wenzel-lab/light-sheet-microscope/adjustable_slit.md

# Adjustable Slit
Cube insert

{{BOM}}

[M3 x 5mm screw]: parts/mech/M3-5.md "{cat:mechanic}"
[M3 x 25mm HEX screw]: parts/mech/HEX-M3-25.md "{cat:mechanic}"
[Nut]: parts/mech/nuts.md "{cat:mechanic}"
[Blades]: parts/mech/blade.md "{cat:mechanic}"

[2.5mm Ball-end Allen key]: parts/tools/2.5mmBallEndAllenKey.md "{cat:tool}"

[Compliant-slit flex - cap]: models/Adjustable_slit/Compliant_slit_insert_V2-cap_layer.stl "{previewpage}"
[Compliant-slit flex - layer 1]: models/Adjustable_slit/Compliant_slit_insert_V2-flex_layer1.stl "{previewpage}"
[Compliant-slit flex - layer 2]: models/Adjustable_slit/Compliant_slit_insert_V2-flex_layer2.stl "{previewpage}"
[Slit Knob]: models/Adjustable_slit/Adjustable-Slit-Knob.stl "{previewpage}"



This flex mechanism helps to control the pass of the light beam by adjusting the top knob.

>! This component is still being tested

#Assembly

## Step 1:
Take the [Compliant-slit flex - layer 1]{qty: 1, cat: PrintedPart} and join it with the [Compliant-slit flex - layer 2]{qty: 1, cat: PrintedPart}, leaving the [Blades]{qty:1} and the [HEX screw][M3 x 25mm HEX screw]{qty:1} in the middle of them. The idea is to leave captured the head of the screw and the sharp edges of the blades in the center.

## Step 2;
Put two [M3 x 5mm screw]{qty: 1} through the assembled piece to hold the blades previously inserted and tight with the [2.5mm Ball-end Allen key]{qty:1}.

## Step 3:
Place the [cap][Compliant-slit flex - cap]{qty: 1, cat: PrintedPart}, closing the mechanism.

## Step 4:
Paste the [Knob][Slit Knob]{qty: 1, cat: PrintedPart} with the screw tip using a strong glue.

##Step 5: Put it in a cube!

Take one of your [UC2 cubes](UC2files.md) and place your assembled piece in it. You can purchase the cube or 3D print it, either option works fine.
