wenzel-lab/light-sheet-microscope/control-Interface.md

# Laser Control Interface

##To assemble this piece, go to our "laser illumination" documentation

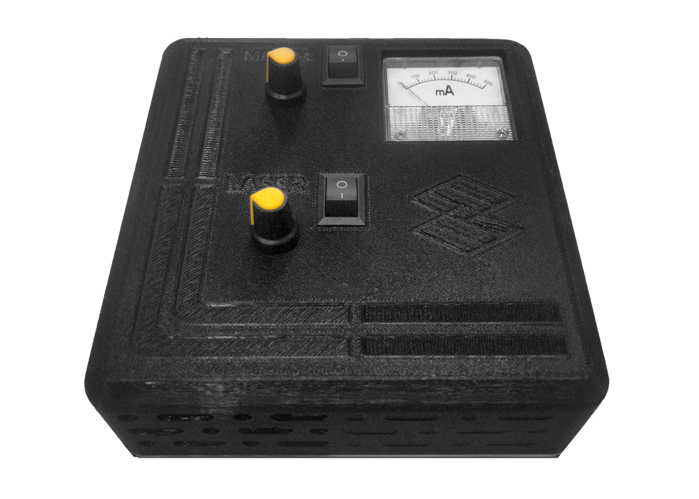
[picture p37: images/control-Interface/control-Interface.jpg]


##

>i **[Link](https://librehub.github.io/fiber-coupled-laser-illumination/assembly.html)** 
>i
>i [Low-cost, modular fiber-coupled laser illumination](https://librehub.github.io/fiber-coupled-laser-illumination/assembly.html)
