wenzel-lab/light-sheet-microscope/Power_lens_XY_aligner.md

# Power Lens XY aligner

Cube insert

{{BOM}}

[M3 x 25 mm hex head screw]: parts/mech/HEX-M3-25.md "{cat:mechanic}"

[Heat insert]: parts/mech/Hinsert.md "{cat:mechanic}"

[Soldering iron]: parts/tools/soldiron.md "{cat:tool}"

[Linear Beam Generator Lens]: parts/optics/Linear-beam-generator-lens.md "{cat:optical}"

[Power Lens XY aligner base]: models/Power-Lense-XY-aligner/Power-Lens-XY-aligner-base.stl "{previewpage}"

[Power Lens XY aligner A-Adapter]:models/Power-Lense-XY-aligner/Power-Lens-XY-aligner-A-Adapter.stl "{previewpage}"



This component is designed to be used inside a UC2 cube, allowing for better laser beam positioning through XY control.

#Assembly: 
##Screws {pagestep}

- Place 2 [heat inserts][Heat insert]{qty:2} into the [XY aligner base][Power Lens XY aligner base]{qty: 1, cat:printedpart} using the [Soldering iron]{qty:1}

- Screw the [hex head screws][M3 x 25 mm hex head screw]{qty:2}



##Lens Adapter {pagestep}
Place the springs and screw the [A-Adapter][Power Lens XY aligner A-Adapter]{qty: 1, cat:printedpart} 



##Lens {pagestep}

Place the [Lens][Linear Beam Generator Lens]{qty:1}  in the  [A-Adapter].

>! **Caution** 
>!
>! Do not touch the lens directly to avoid getting it dirty or scratched.

## Put it in a cube!:{pagestep}

Take one of your [UC2 cubes](UC2files.md) and place your assembled piece in it. You can purchase the cube or 3D print it, either option works fine.
