wenzel-lab/light-sheet-microscope/Prepare.md

#Prepare the pieces

* ### [Print the plastic Parts](printing.md)

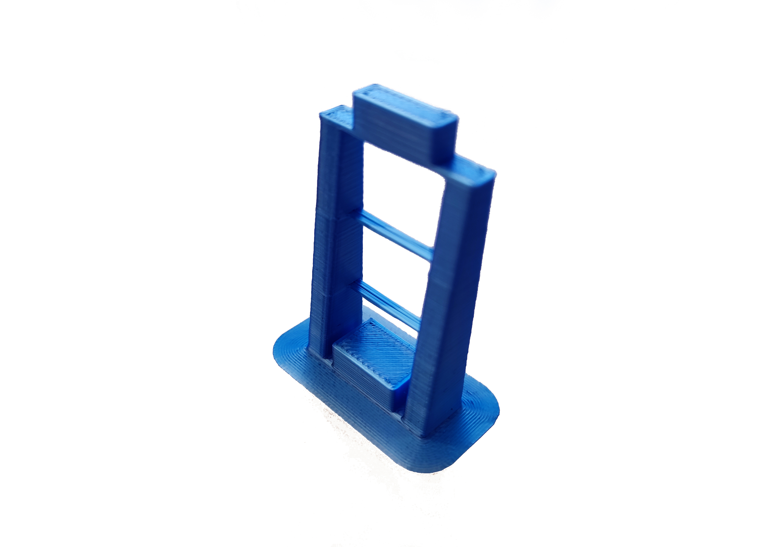
[picture p44: images/Tools-and-Parts/just_leg_test.jpg]


* ### [Sanding screw tips](Sanding.md)

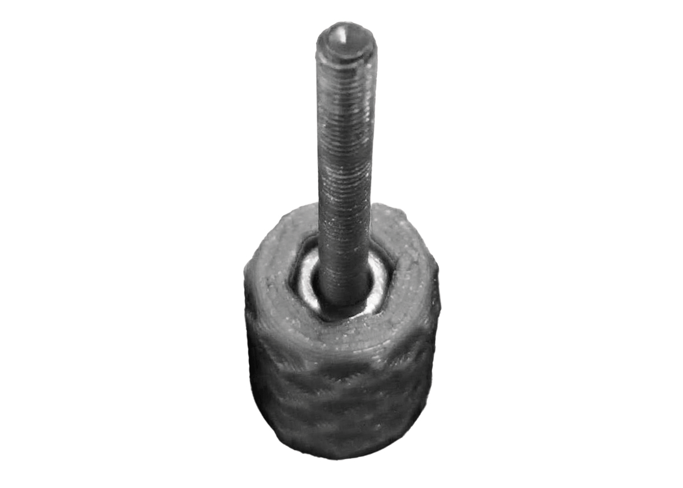
[picture p45: images/Sanding/sand.gif]
