wenzel-lab/light-sheet-microscope/images/Kinematic_Mirrors/Completed.jpg

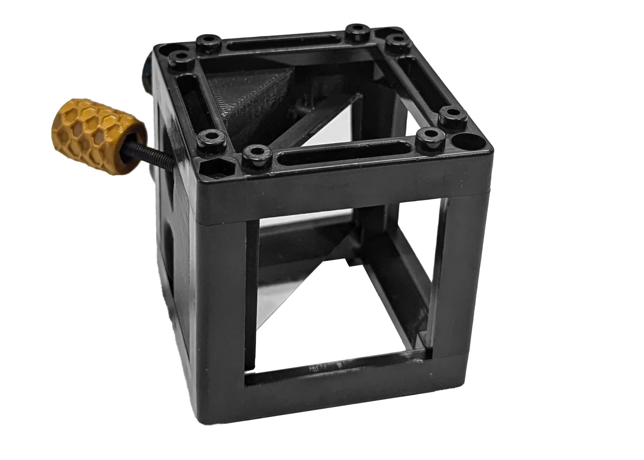
images/Kinematic_Mirrors/Completed.jpg
