wenzel-lab/light-sheet-microscope/images/Kinematic_Mirrors/Holder-and-Mirror.jpg

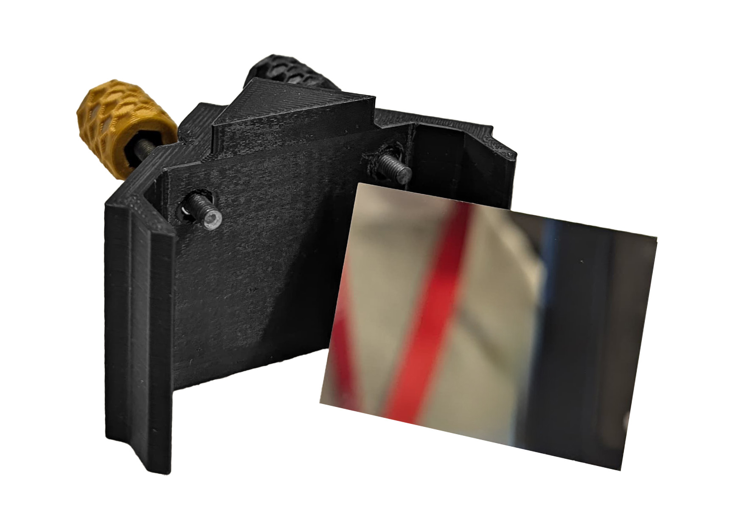
images/Kinematic_Mirrors/Holder-and-Mirror.jpg
