wenzel-lab/light-sheet-microscope/parts/tools/screwdriver.md

# Screwdriver

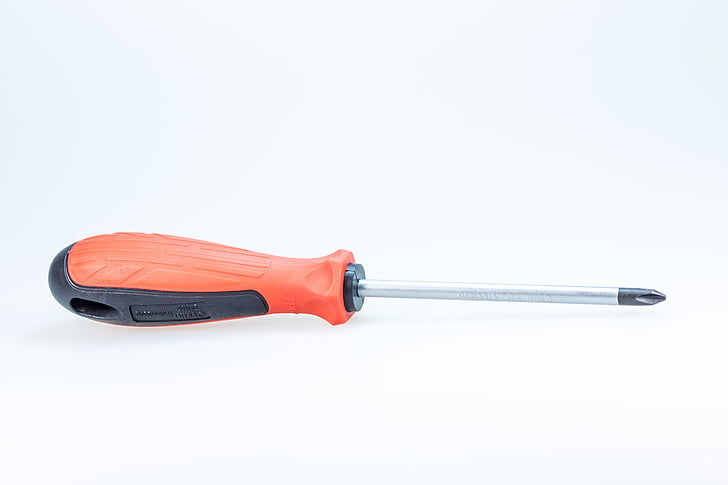
[picture p66: images/Tools-and-Parts/screwdriver.jpg]


*Supplier:* [Aliexpress](https://es.aliexpress.com/item/1005006019454539.html)
