wenzel-lab/light-sheet-microscope/parts/tools/soldiron.md

# Soldering iron

Handheld tool usually used for joining or repairing electronic components. It consists of a heated metal tip attached to a handle. The tip is heated using electrical power, typically supplied via a power cord. Soldering irons come in different wattage's and tip sizes to accommodate various soldering tasks.

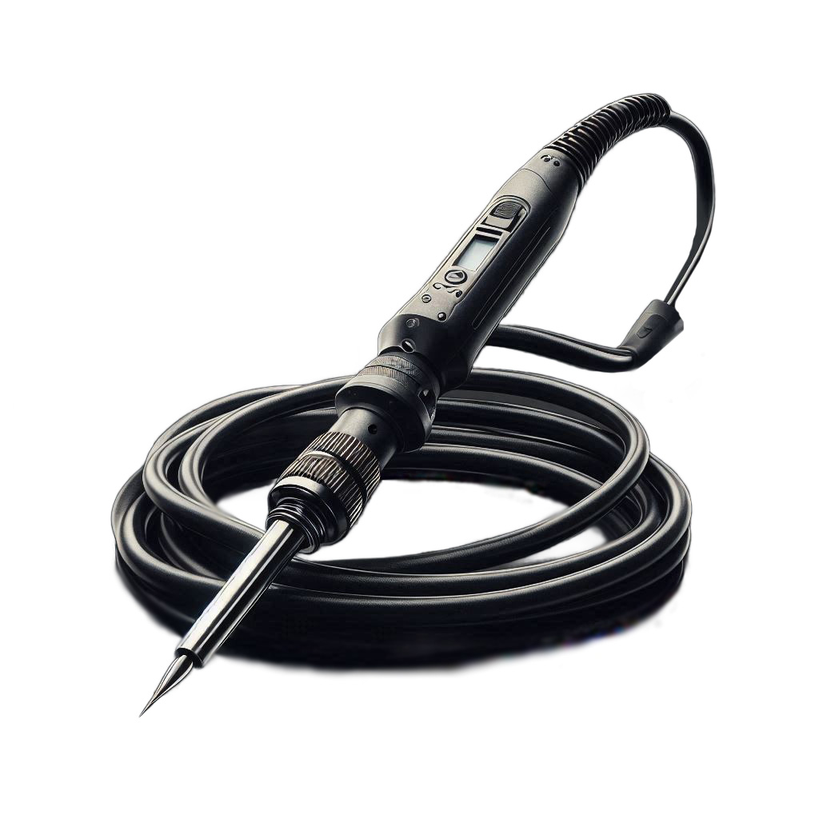
[picture p67: images/Tools-and-Parts/soldering.jpeg]
