wenzel-lab/light-sheet-microscope/parts/tools/crimper.md

# Crimper

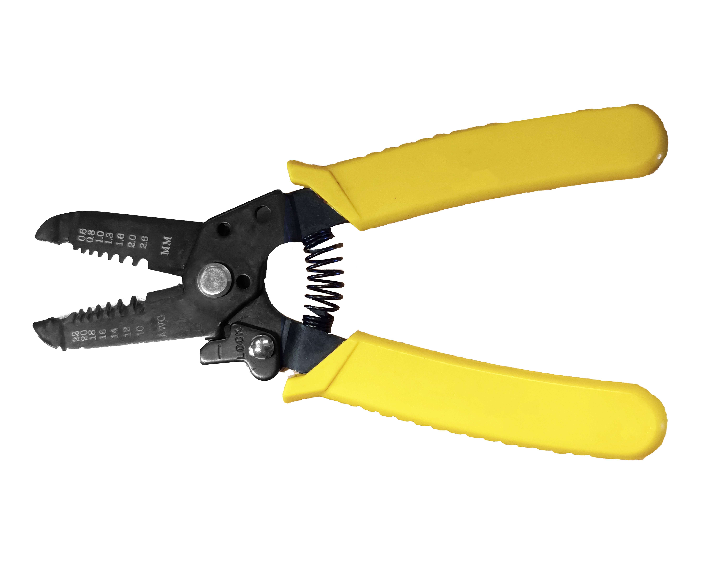
[picture p70: images/Tools-and-Parts/Crimper.jpg]


*Supplier:* [Altronics](https://altronics.cl/alicate-pelacables-tuosen-11390)
