wenzel-lab/light-sheet-microscope/parts/tools/pliers.md

# Needle-nose plier

Hand tool with long, slender jaws that taper to a fine point.
Used for gripping and manipulating small objects in tight or hard-to-reach spaces.

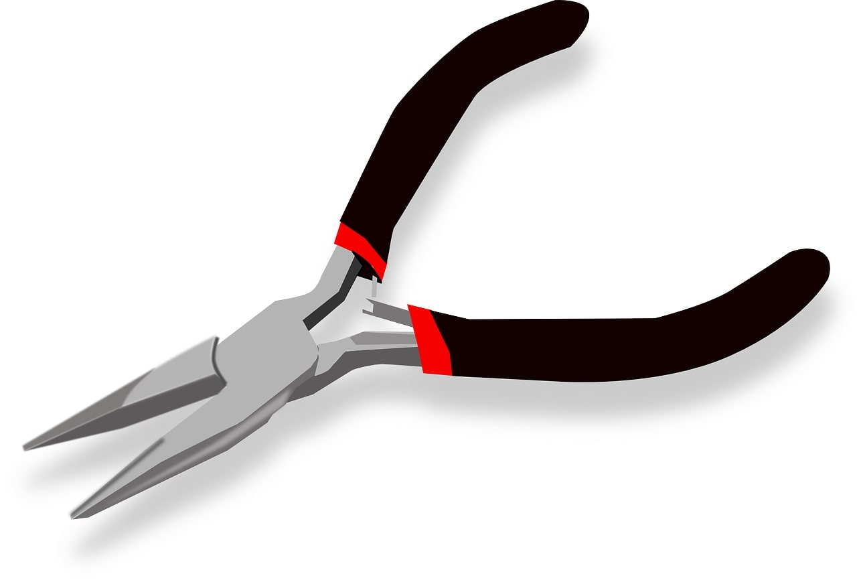
[picture p71: images/Tools-and-Parts/pliersLCC.jpg]


*Supplier:* [Easy](https://www.easy.cl/alicate-de-punta-6-mk-0104-makawa-1287232/p)
