wenzel-lab/light-sheet-microscope/parts/tools/tweezers.md

# Tweezers

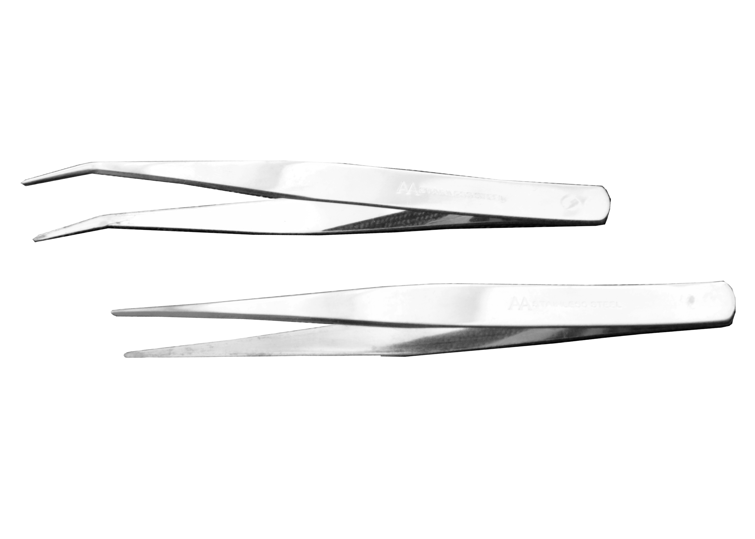
[picture p72: images/Tools-and-Parts/Tweezers.jpg]


Small, handheld tools with two arms and pointed tips, used for picking up and manipulating small objects with precision.
