wenzel-lab/light-sheet-microscope/images/Tools-and-Parts/hexagon_tape.jpg

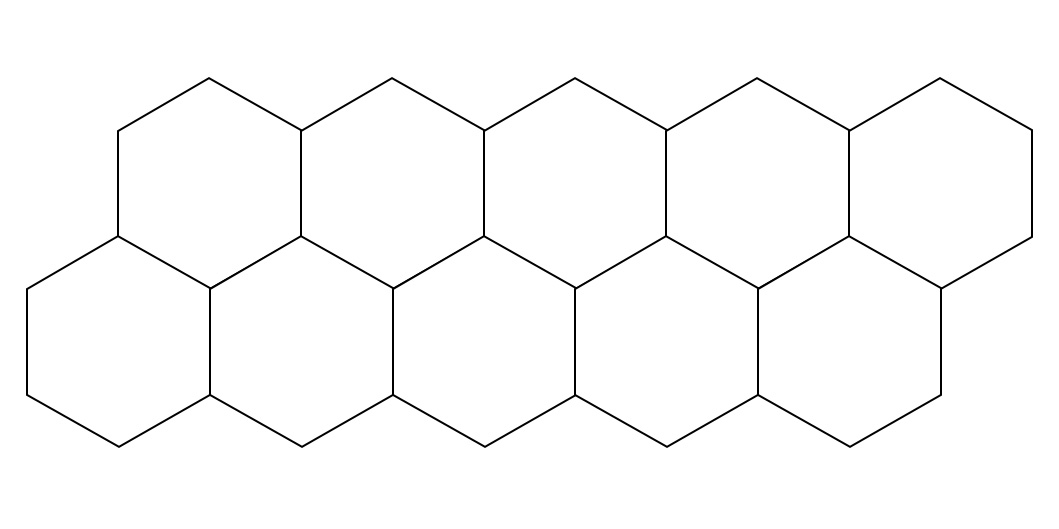
images/Tools-and-Parts/hexagon_tape.jpg
