wenzel-lab/light-sheet-microscope/images/Tools-and-Parts/laser_cutter.png

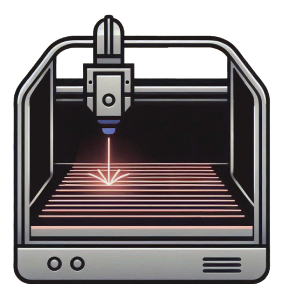
images/Tools-and-Parts/laser_cutter.png
