wenzel-lab/light-sheet-microscope/images/Tools-and-Parts/light-led.jpg

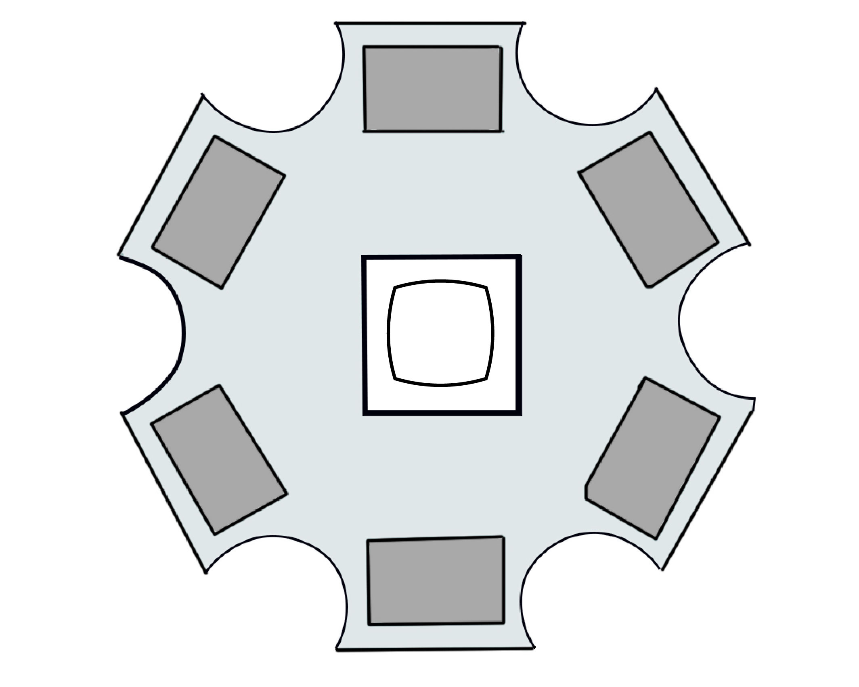
images/Tools-and-Parts/light-led.jpg
