wenzel-lab/light-sheet-microscope/images/Tools-and-Parts/strobe_cable.jpg

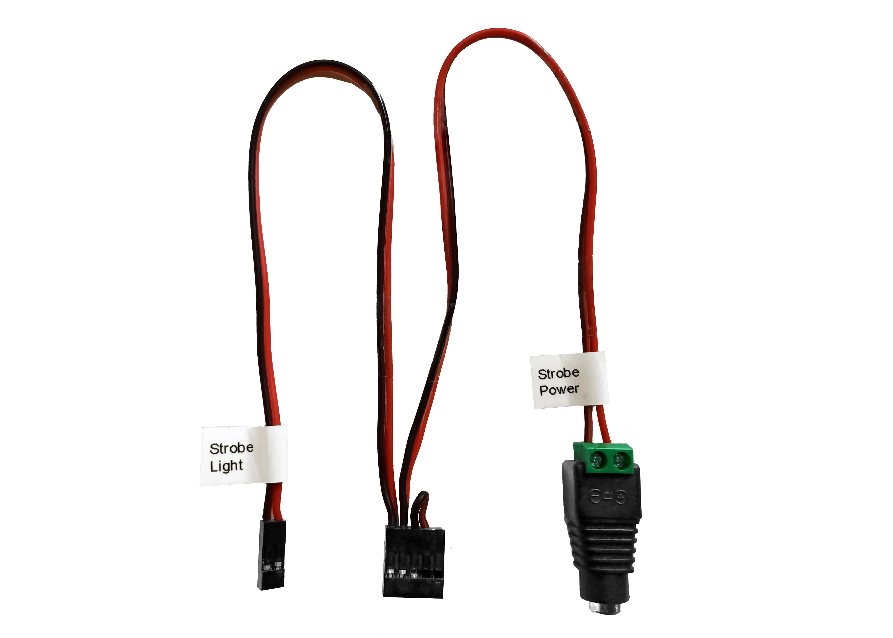
images/Tools-and-Parts/strobe_cable.jpg
