wenzel-lab/light-sheet-microscope/models/Filter_Holder/Holder-Filter-Slide-25-mm.stl

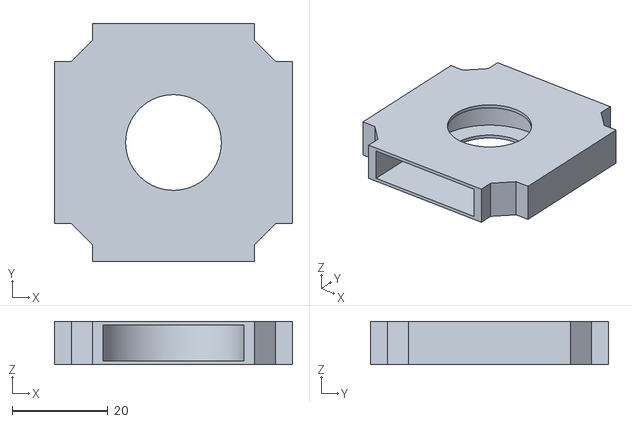
[picture p92: CAD file, 2024-07-26]
models/Filter_Holder/Holder-Filter-Slide-25-mm.stl
49.8 x 49.8 x 9.10
