wenzel-lab/light-sheet-microscope/models/Kinematic_Mirrors/Diagonal-Kinematic-Mount-LIBREhub.stl

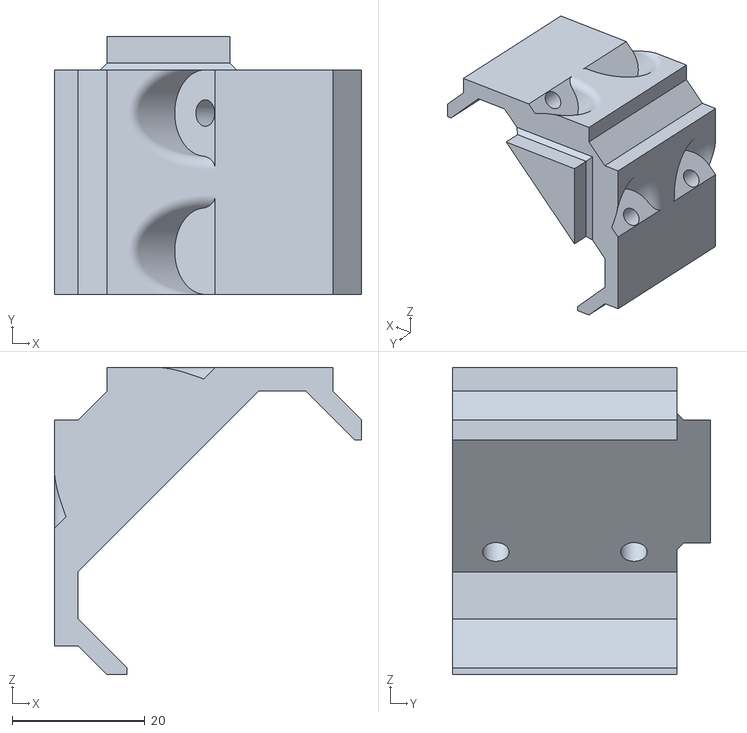
[picture p93: CAD file, 2024-09-17]
models/Kinematic_Mirrors/Diagonal-Kinematic-Mount-LIBREhub.stl
46.2 x 38.8 x 46.2
