wenzel-lab/light-sheet-microscope/models/Lens_Holder/Flexure_cylindrical_lens_holder-cyl-lens-holder-flex.stl

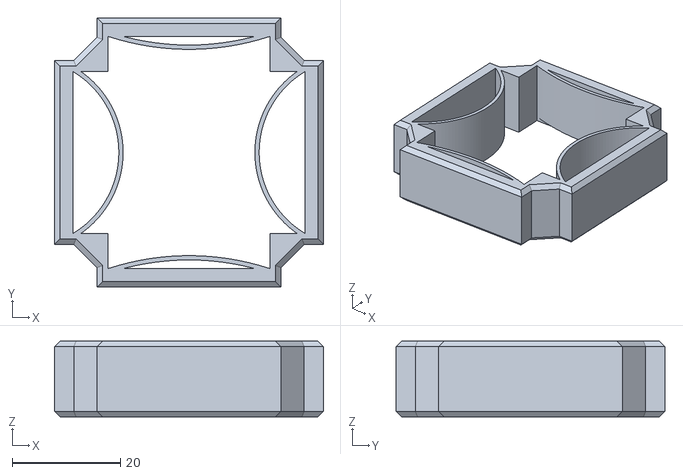
[picture p94: CAD file, 2024-07-26]
models/Lens_Holder/Flexure_cylindrical_lens_holder-cyl-lens-holder-flex.stl
49.8 x 49.8 x 14.0
