wenzel-lab/light-sheet-microscope/models/Power-Lense-XY-aligner/Power-Lens-XY-aligner-A-Adapter.stl

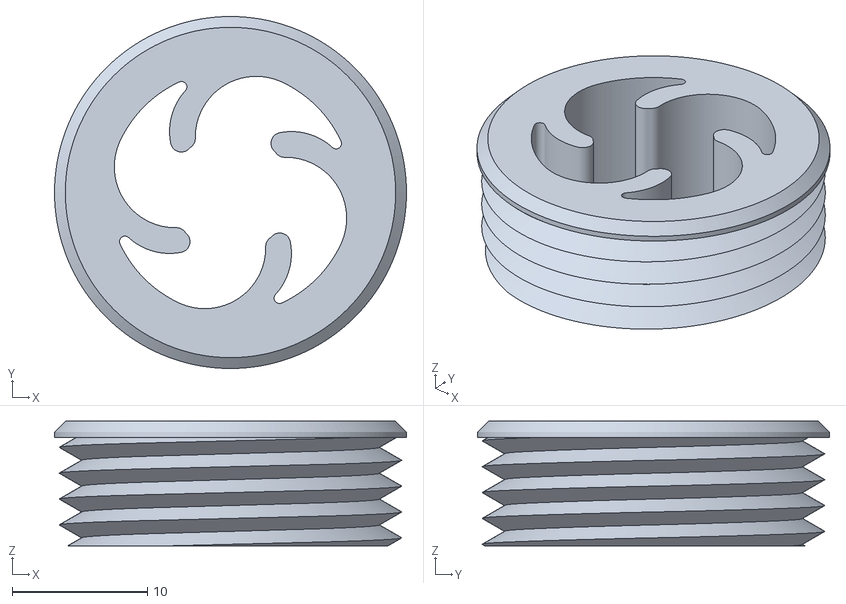
[picture p95: CAD file, 2024-07-26]
models/Power-Lense-XY-aligner/Power-Lens-XY-aligner-A-Adapter.stl
26.0 x 26.0 x 9.20
