wenzel-lab/light-sheet-microscope/models/SM1_holder/UC2-SM2_adaptor - 5mm-pinhole-SM1.stl

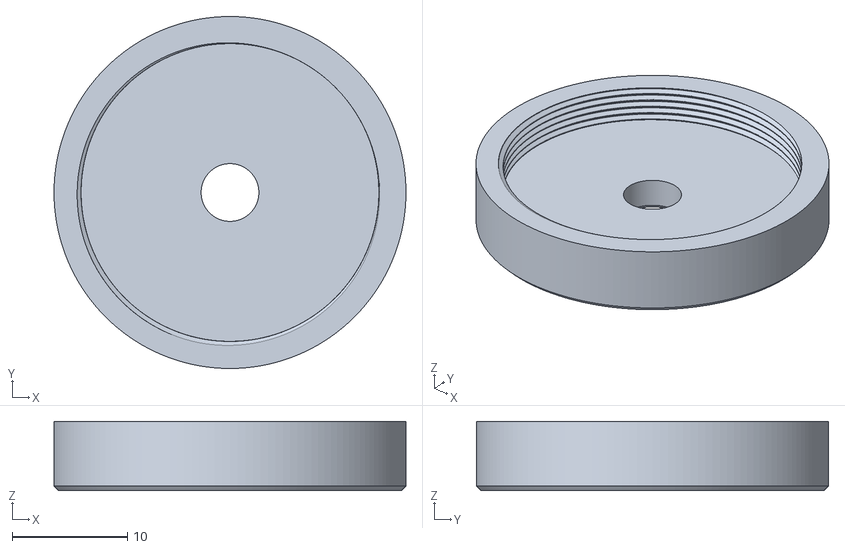
[picture p96: CAD file, 2024-07-26]
models/SM1_holder/UC2-SM2_adaptor - 5mm-pinhole-SM1.stl
30.5 x 30.5 x 6.00
