wenzel-lab/light-sheet-microscope/models/Stepper_Motor_Container/adapter_LBX40_21H4U.stp

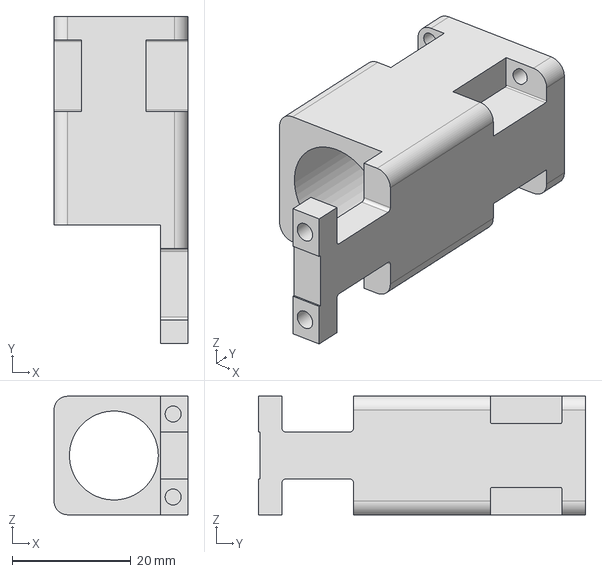
[picture p97: CAD file, 2024-09-25]
models/Stepper_Motor_Container/adapter_LBX40_21H4U.stp
22.6 x 55.2 x 20.0 mm
