wenzel-lab/light-sheet-microscope/models/Adjustable_slit/Compliant_slit_insert_V2-flex_layer1.stl

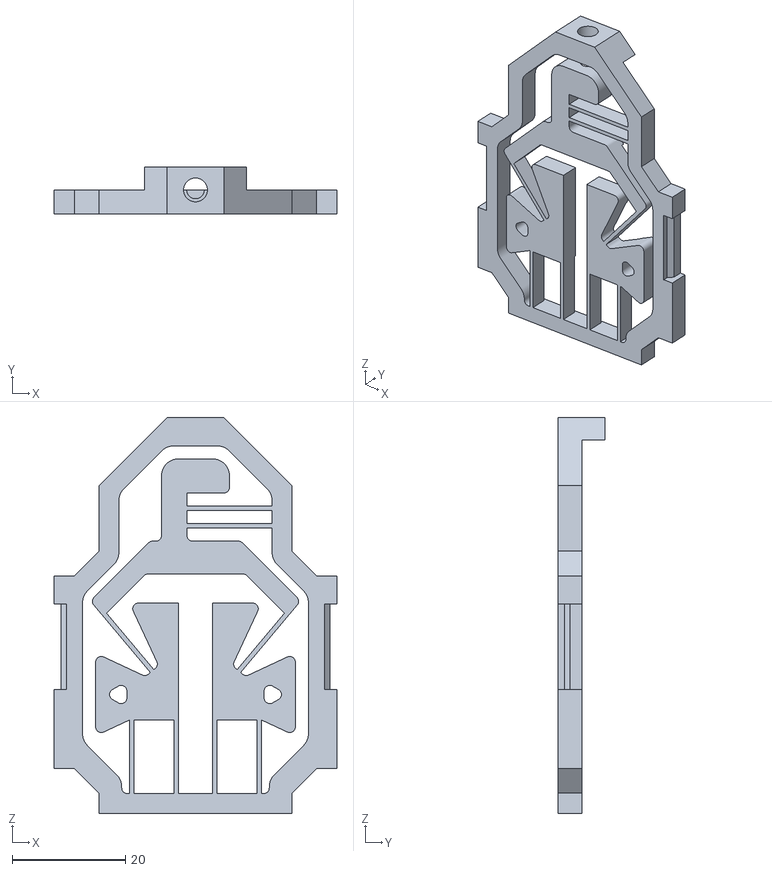
[picture p98: CAD file, 2024-07-26]
models/Adjustable_slit/Compliant_slit_insert_V2-flex_layer1.stl
49.8 x 8.20 x 69.8
