wenzel-lab/light-sheet-microscope/models/Base_Cube/Base_puzzle.stl

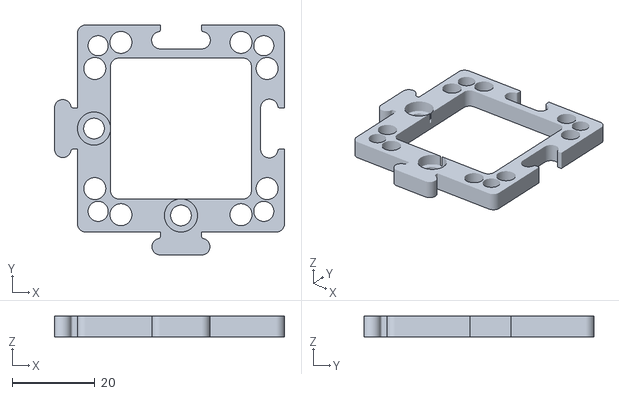
[picture p99: CAD file, 2024-09-17]
models/Base_Cube/Base_puzzle.stl
55.5 x 55.5 x 5.00
