wenzel-lab/light-sheet-microscope/models/Kinematic_Mirrors/Knob.stl

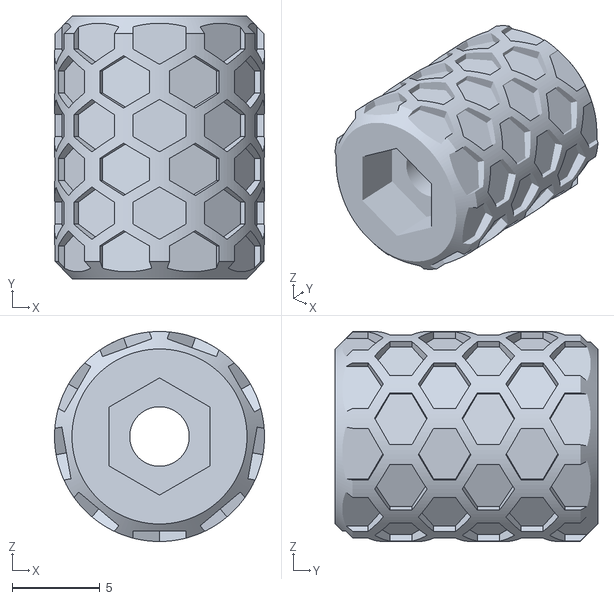
[picture p100: CAD file, 2024-09-17]
models/Kinematic_Mirrors/Knob.stl
12.0 x 15.0 x 12.0
