wenzel-lab/light-sheet-microscope/models/Stepper_Motor_Container/stepper.stl

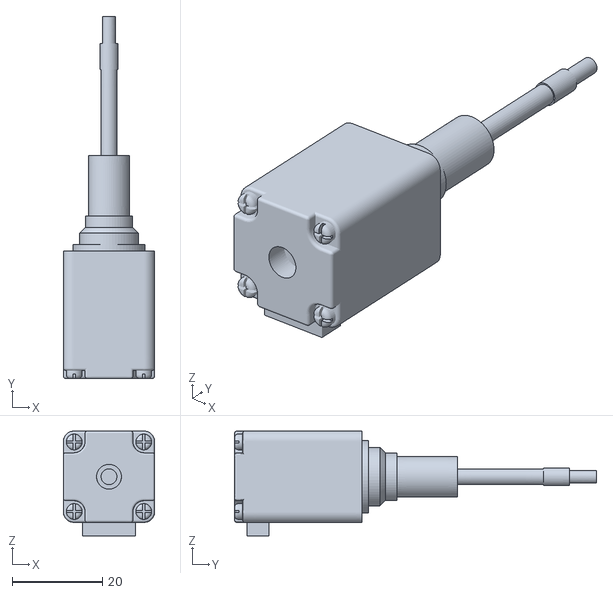
[picture p101: CAD file, 2024-09-25]
models/Stepper_Motor_Container/stepper.stl
20.2 x 80.1 x 23.2
