wenzel-lab/light-sheet-microscope/models/Kinematic_Mirrors/Side-Kinematic-Mount-LIBREhub.stl

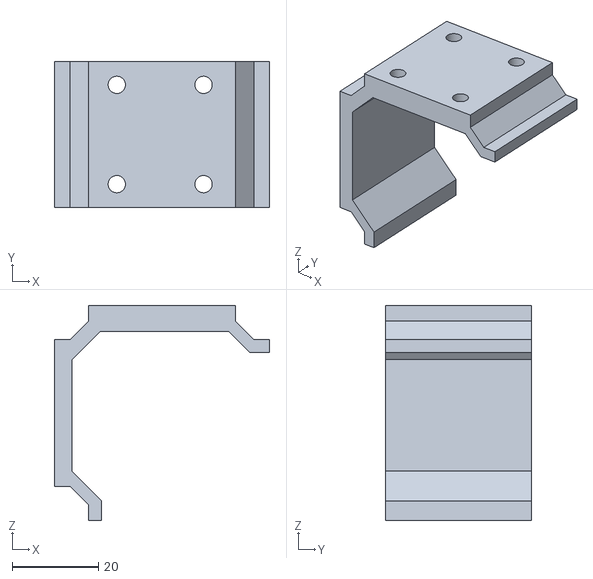
[picture p102: CAD file, 2024-09-17]
models/Kinematic_Mirrors/Side-Kinematic-Mount-LIBREhub.stl
49.8 x 33.8 x 49.8
