wenzel-lab/light-sheet-microscope/models/Stepper_Motor_Container/LightSheet_Remake-New_Axis_Cube.stl

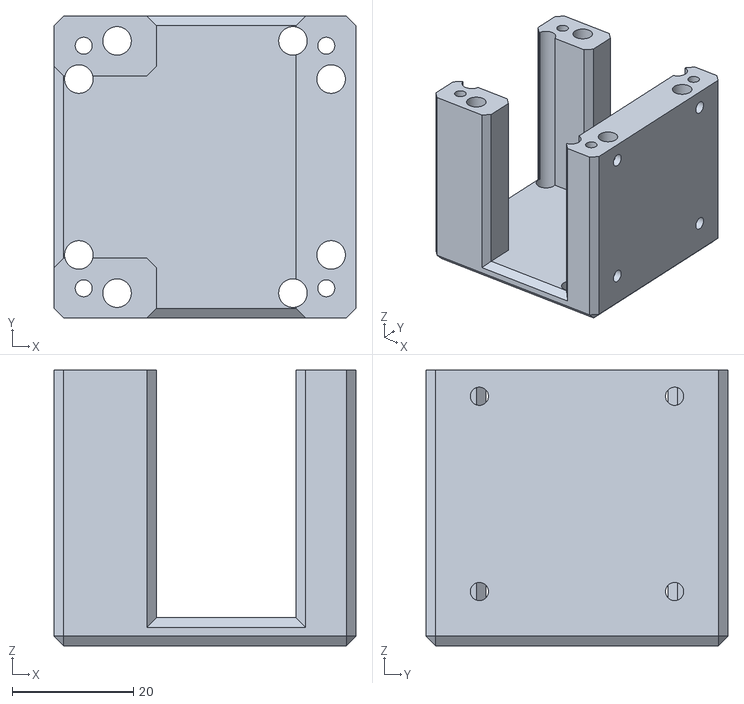
[picture p103: CAD file, 2024-07-26]
models/Stepper_Motor_Container/LightSheet_Remake-New_Axis_Cube.stl
49.8 x 49.8 x 45.4
