wenzel-lab/light-sheet-microscope/models/Kinematic_Mirrors/Diagonal-Mirror-Surface-LIBREhub.stl

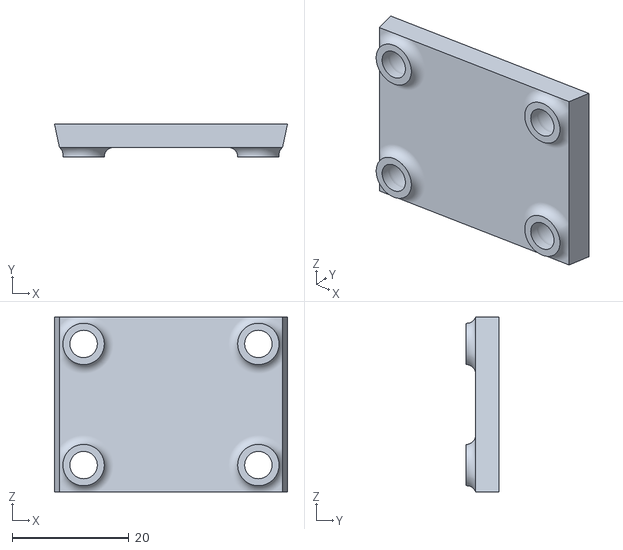
[picture p104: CAD file, 2024-09-17]
models/Kinematic_Mirrors/Diagonal-Mirror-Surface-LIBREhub.stl
40.0 x 5.60 x 30.0
