wenzel-lab/light-sheet-microscope/models/Stepper_Motor_Container/LightSheet_Remake-Inner_Motor_Holder.stl

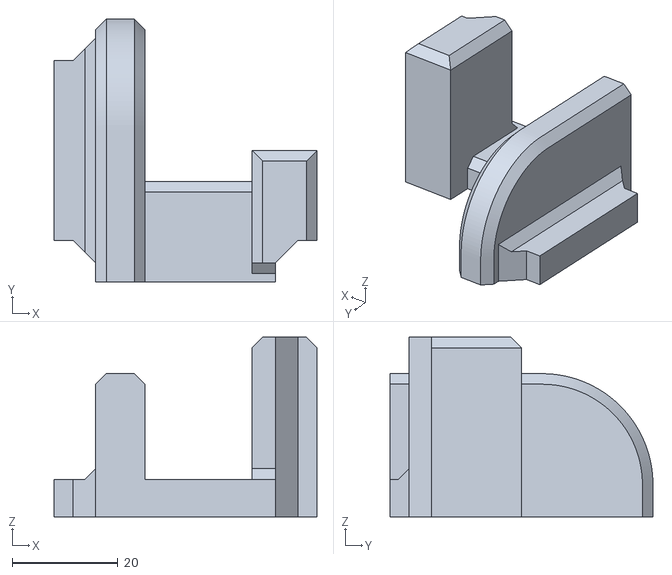
[picture p105: CAD file, 2024-07-26]
models/Stepper_Motor_Container/LightSheet_Remake-Inner_Motor_Holder.stl
49.8 x 49.8 x 34.0
