wenzel-lab/light-sheet-microscope/models/Stepper_Motor_Container/LightSheet_Remake-Objective_arm.stl

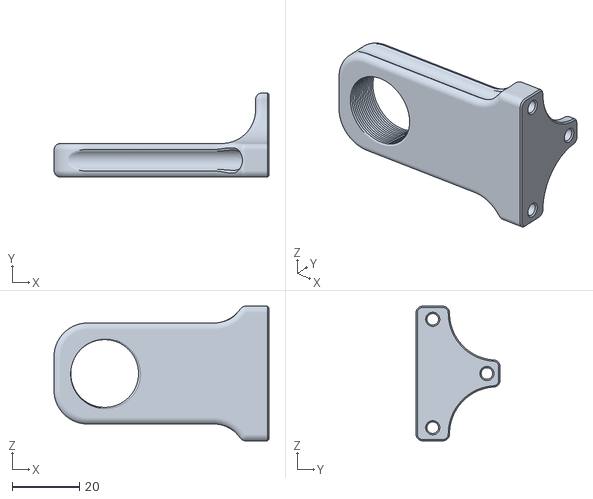
[picture p106: CAD file, 2024-07-26]
models/Stepper_Motor_Container/LightSheet_Remake-Objective_arm.stl
63.8 x 25.0 x 40.0
