wenzel-lab/light-sheet-microscope/models/Stepper_Motor_Container/LightSheet_Remake-New_Axis_Cube_Top.stl

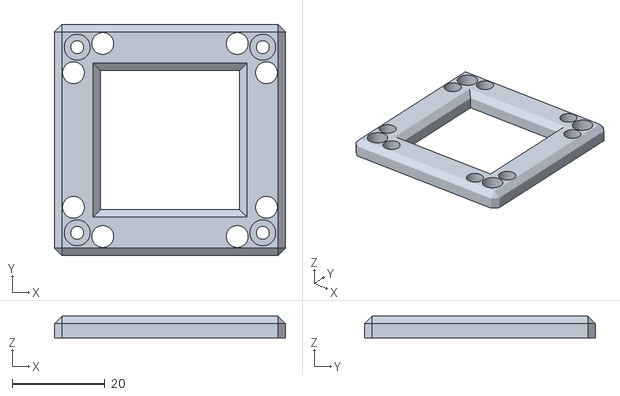
[picture p107: CAD file, 2024-07-26]
models/Stepper_Motor_Container/LightSheet_Remake-New_Axis_Cube_Top.stl
49.8 x 49.8 x 4.65
